NickEngmann/smarthome-reachy-mini/cad/crowpanel-advanced-7in-esp32-p4/preview.png

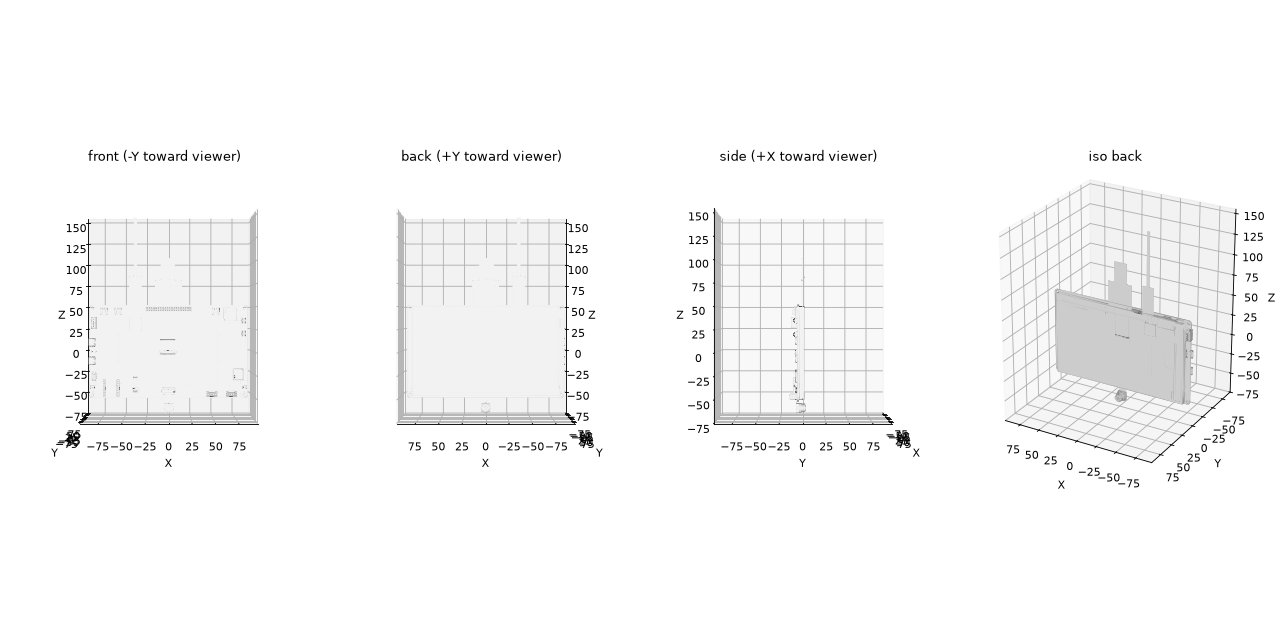
cad/crowpanel-advanced-7in-esp32-p4/preview.png
