NickEngmann/smarthome-reachy-mini/cad/reachy-mini/preview.png

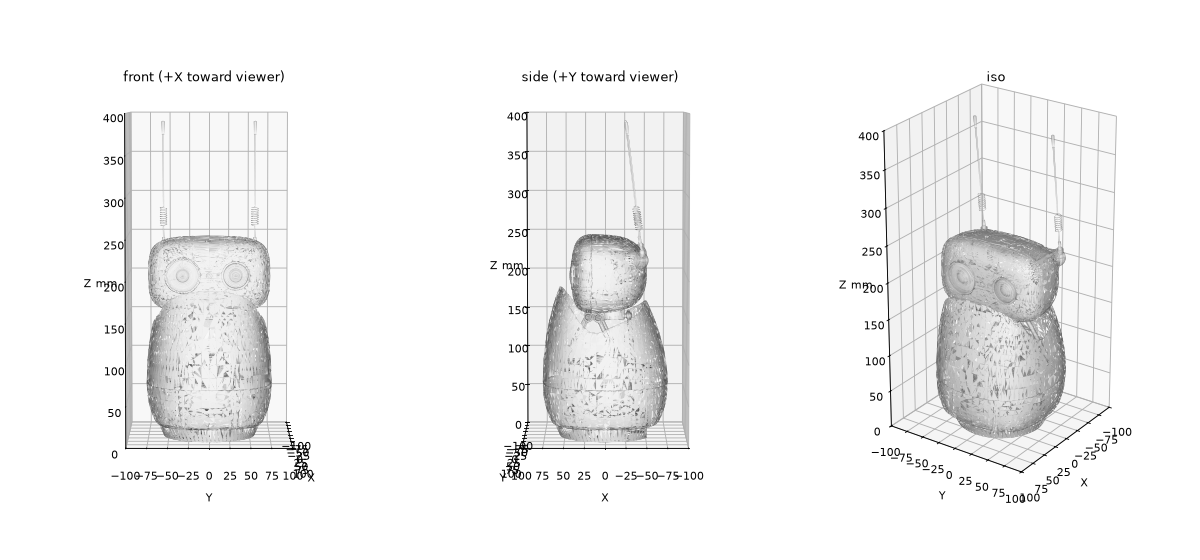
cad/reachy-mini/preview.png
