NickEngmann/smarthome-reachy-mini/hardware/enclosure/out/render/back-closeup.png

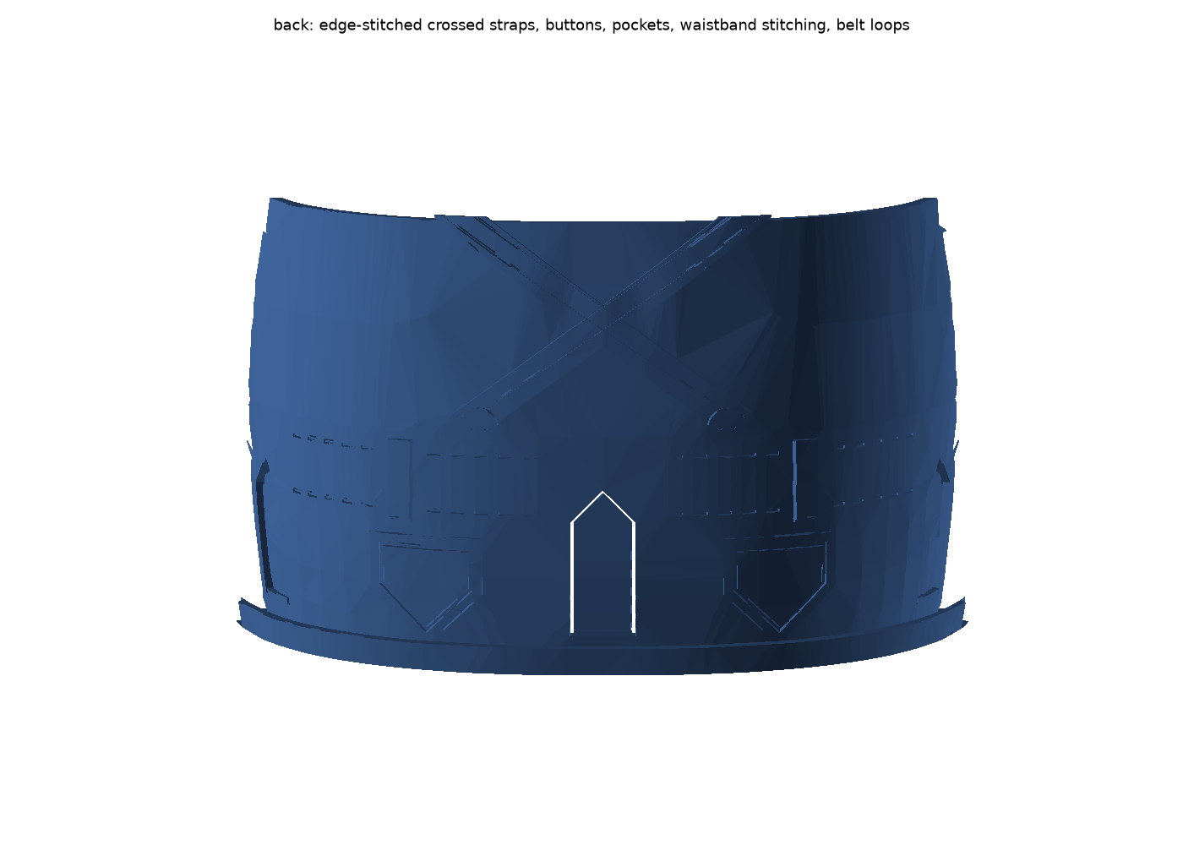
hardware/enclosure/out/render/back-closeup.png
