NickEngmann/smarthome-reachy-mini/hardware/enclosure/out/render/back-three-quarter.png

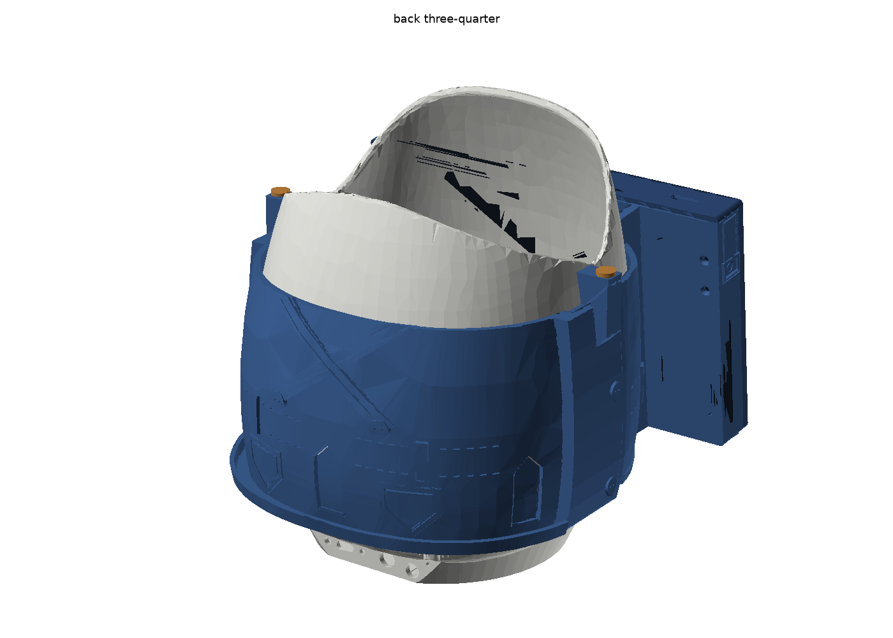
hardware/enclosure/out/render/back-three-quarter.png
