NickEngmann/smarthome-reachy-mini/hardware/enclosure/out/render/back.png

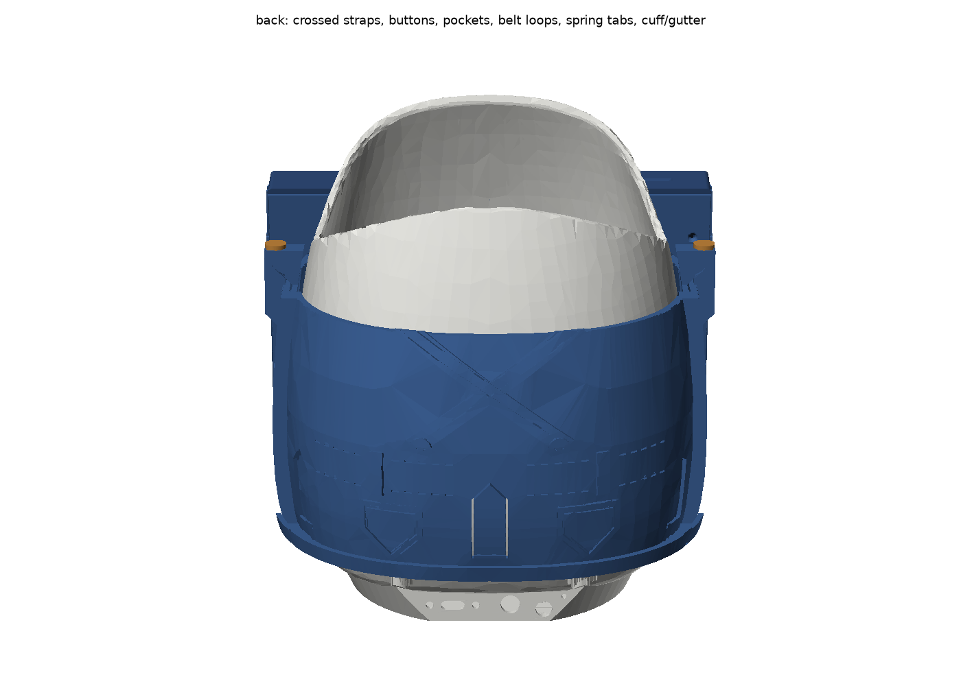
hardware/enclosure/out/render/back.png
