NickEngmann/smarthome-reachy-mini/hardware/enclosure/out/render/bib-closeup.png

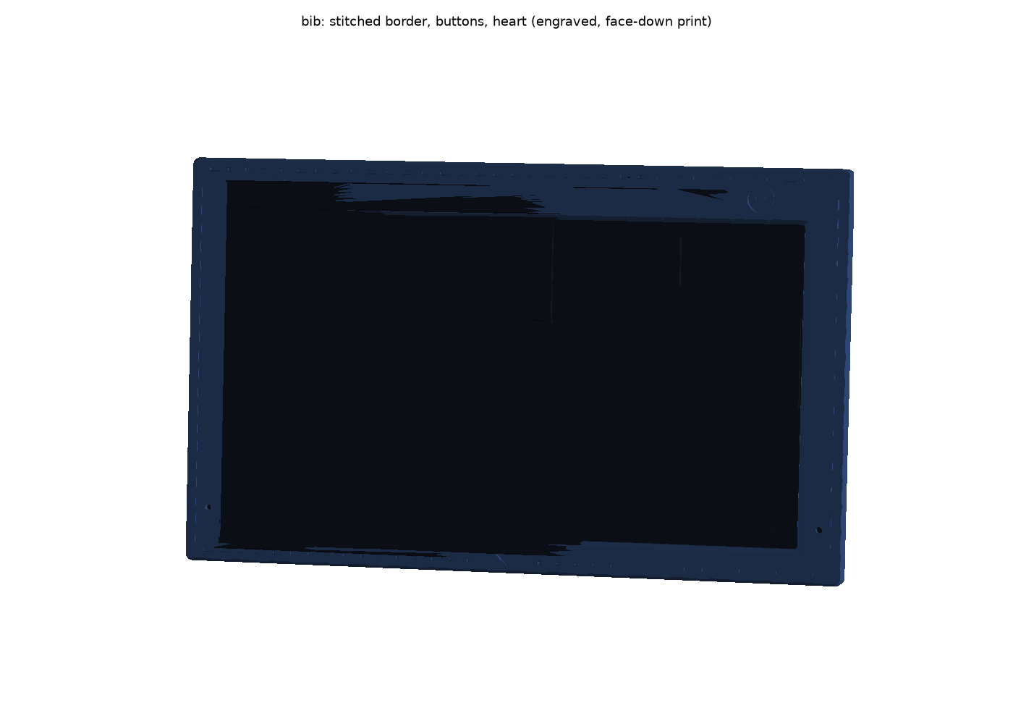
hardware/enclosure/out/render/bib-closeup.png
