NickEngmann/smarthome-reachy-mini/hardware/enclosure/out/render/exploded.png

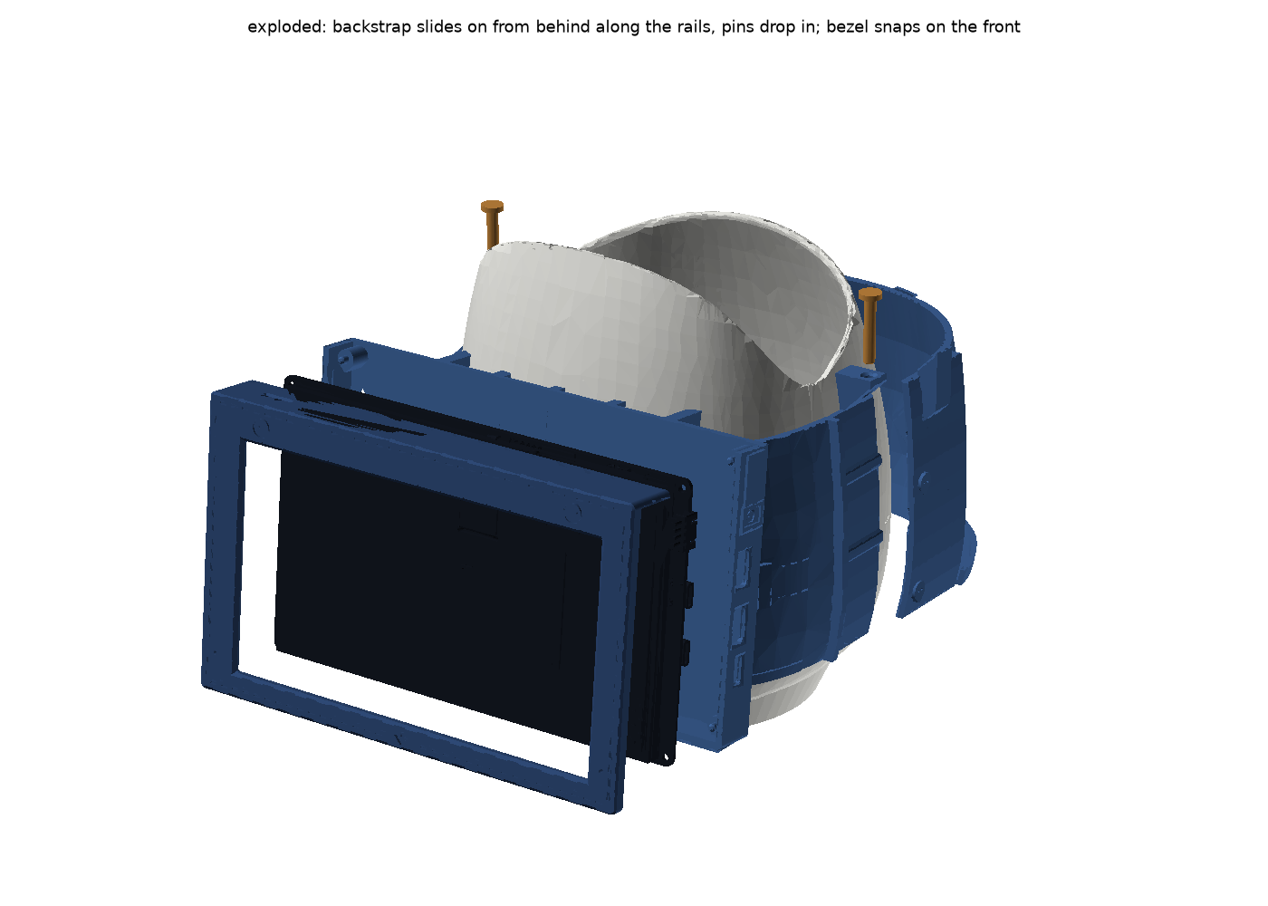
hardware/enclosure/out/render/exploded.png
