NickEngmann/smarthome-reachy-mini/hardware/enclosure/out/render/hero.png

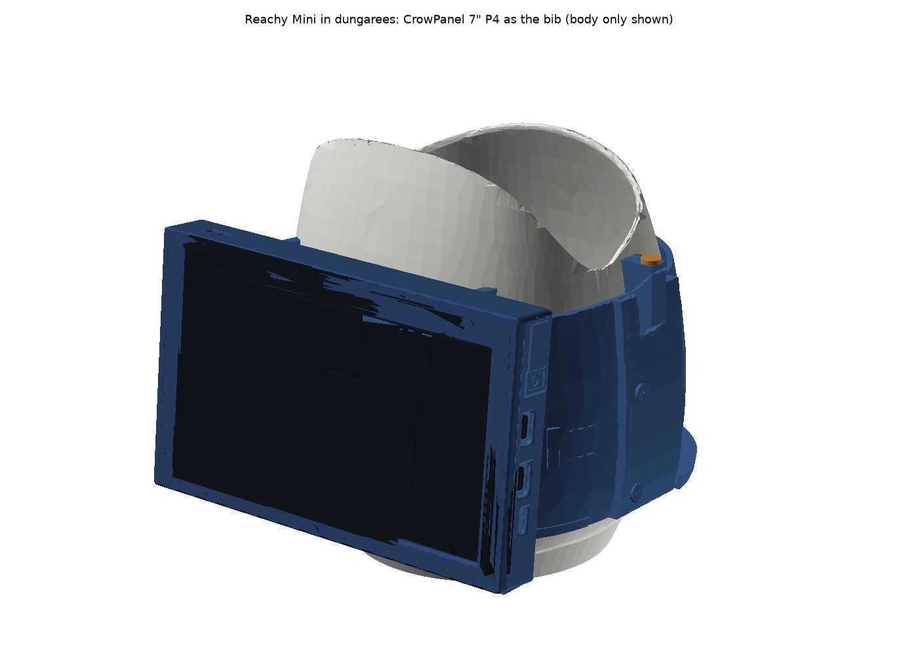
hardware/enclosure/out/render/hero.png
