NickEngmann/smarthome-reachy-mini/hardware/enclosure/out/render/joint-closeup.png

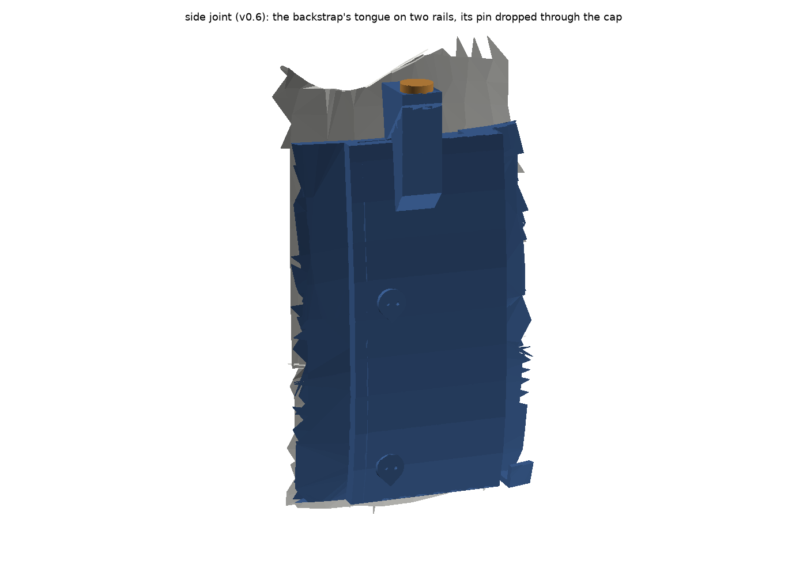
hardware/enclosure/out/render/joint-closeup.png
