NickEngmann/smarthome-reachy-mini/hardware/enclosure/out/render/joint-exploded.png

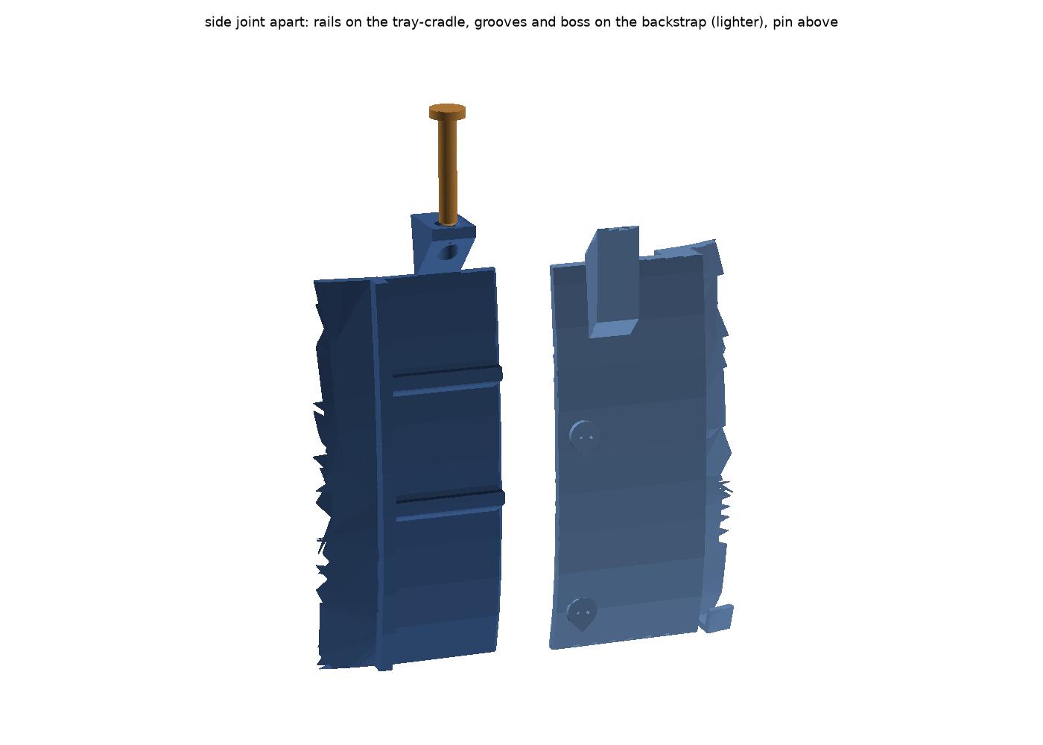
hardware/enclosure/out/render/joint-exploded.png
