NickEngmann/smarthome-reachy-mini/hardware/enclosure/out/render/overalls-cutaway-lifted.png

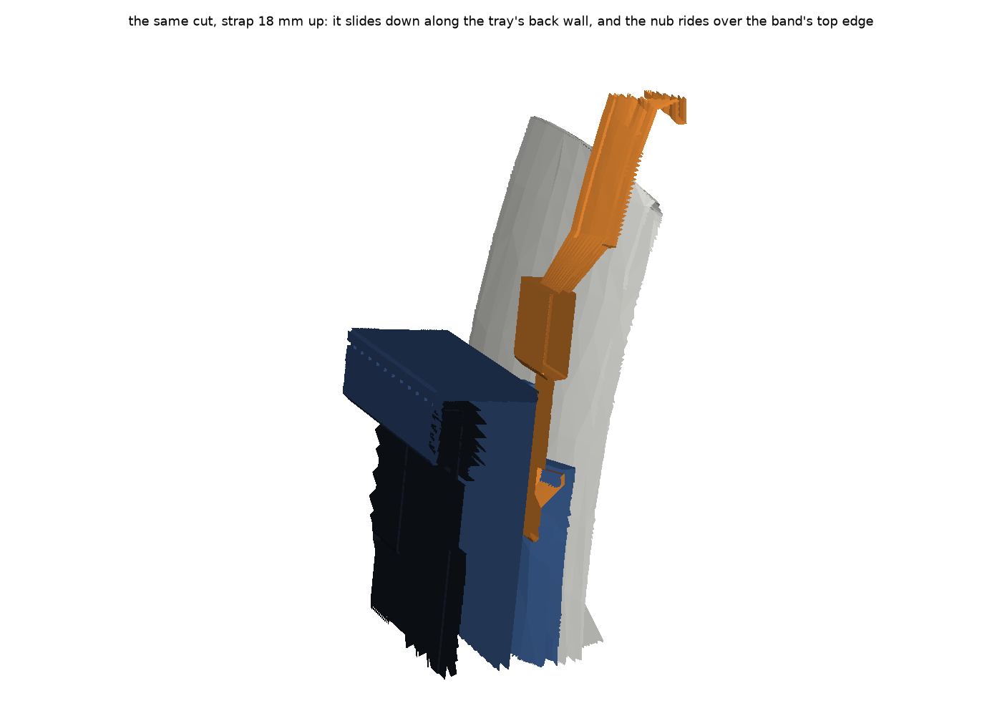
hardware/enclosure/out/render/overalls-cutaway-lifted.png
