NickEngmann/smarthome-reachy-mini/hardware/enclosure/out/render/overalls-fitting.png

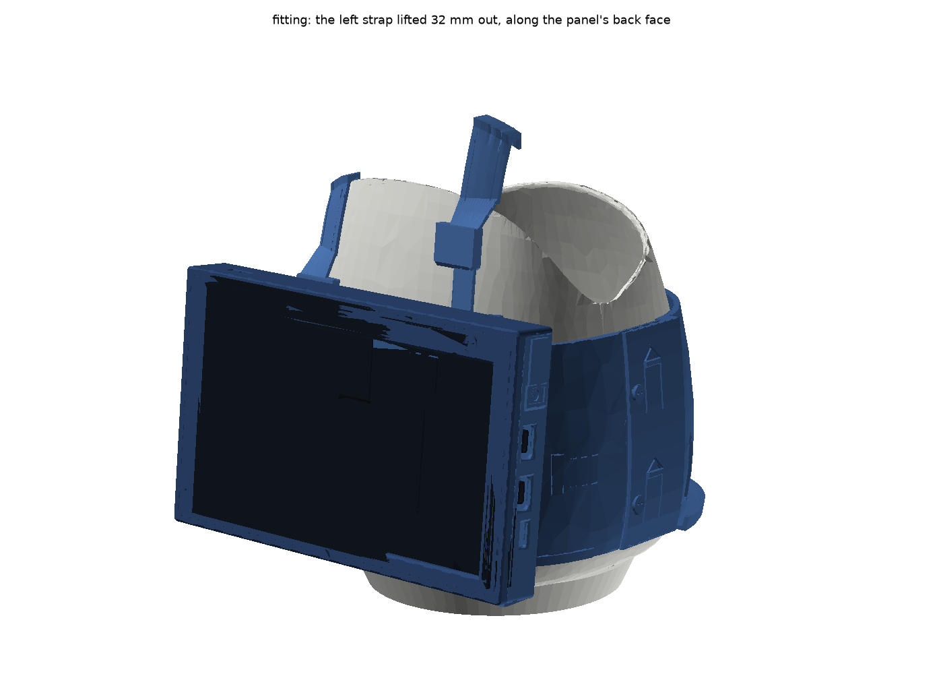
hardware/enclosure/out/render/overalls-fitting.png
