NickEngmann/smarthome-reachy-mini/hardware/enclosure/out/render/overalls-front.png

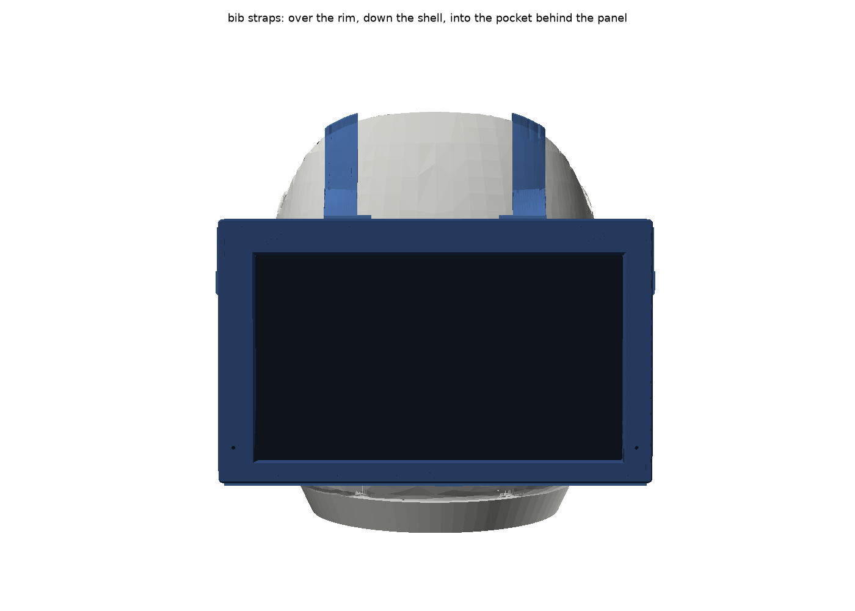
hardware/enclosure/out/render/overalls-front.png
