NickEngmann/smarthome-reachy-mini/hardware/enclosure/out/render/overalls-high.png

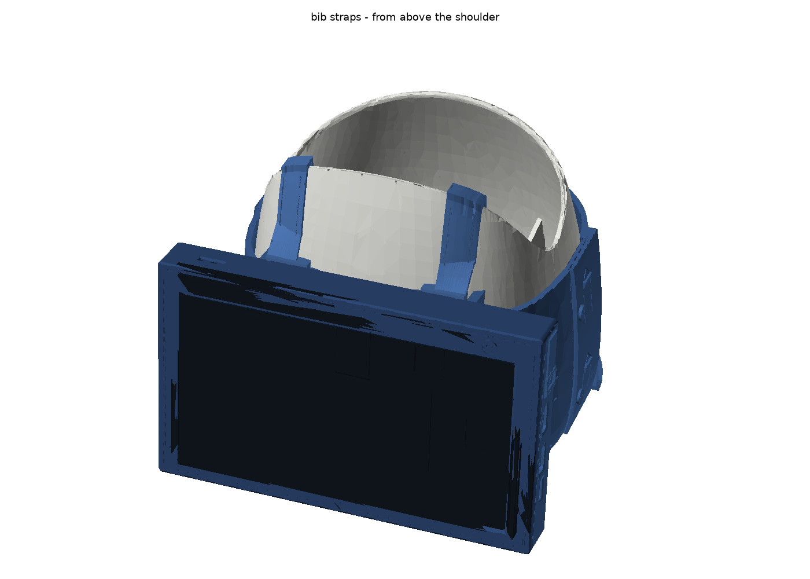
hardware/enclosure/out/render/overalls-high.png
