NickEngmann/smarthome-reachy-mini/hardware/enclosure/out/render/overalls-section-foot.png

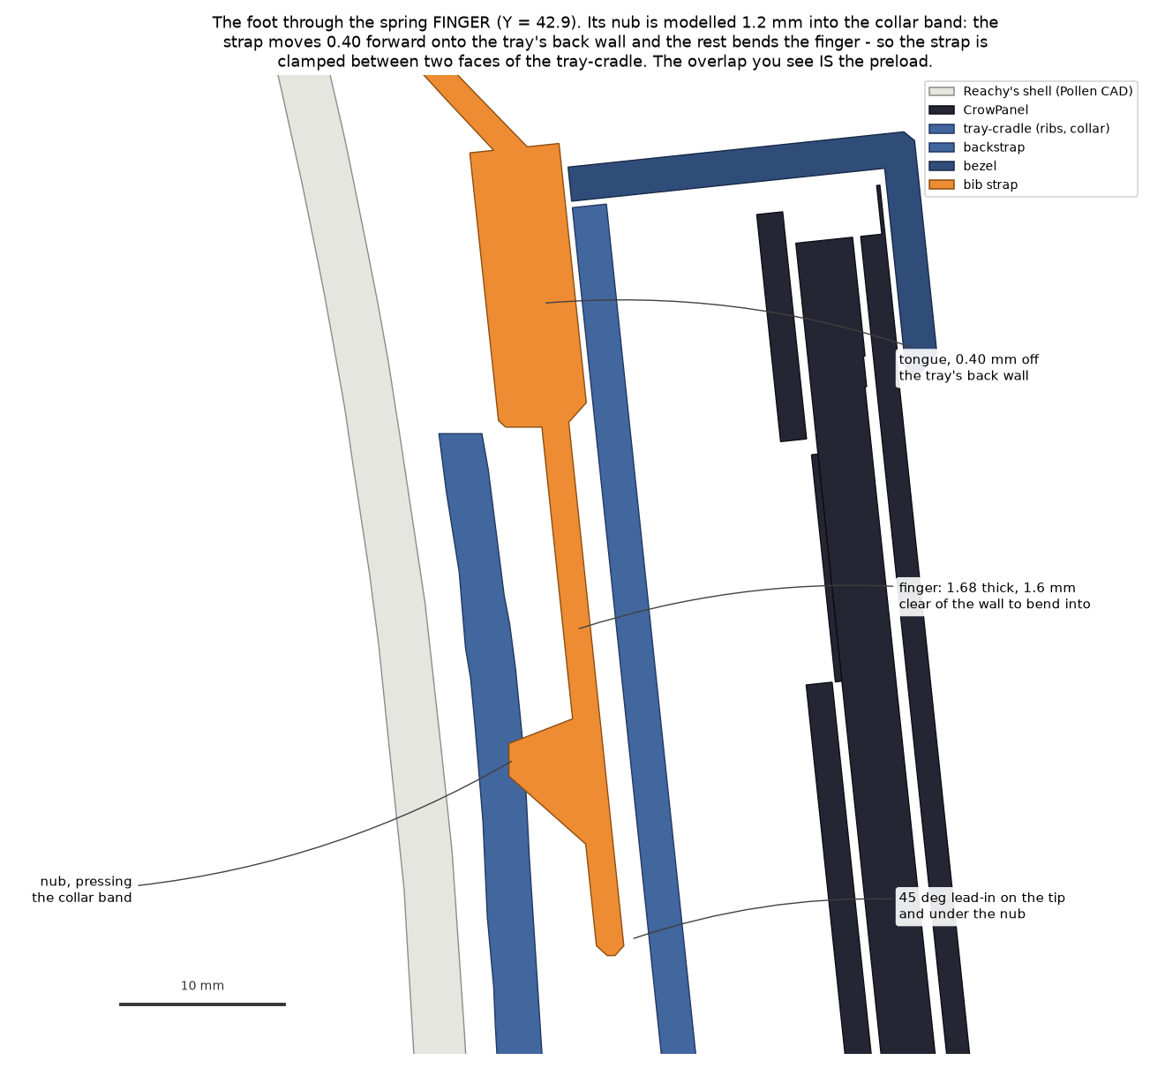
hardware/enclosure/out/render/overalls-section-foot.png
