NickEngmann/smarthome-reachy-mini/hardware/enclosure/out/render/overalls-section-rim.png

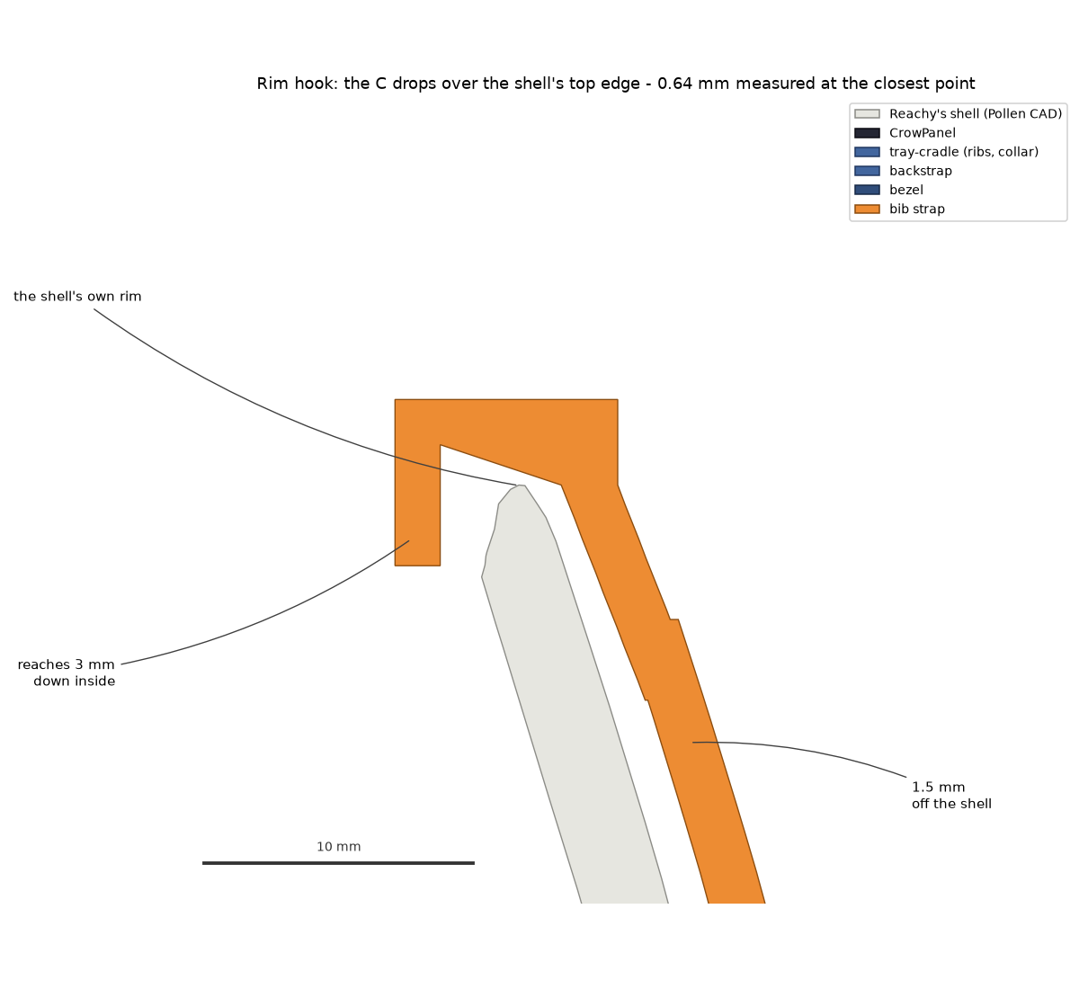
hardware/enclosure/out/render/overalls-section-rim.png
