NickEngmann/smarthome-reachy-mini/hardware/enclosure/out/render/overalls-section-tongue.png

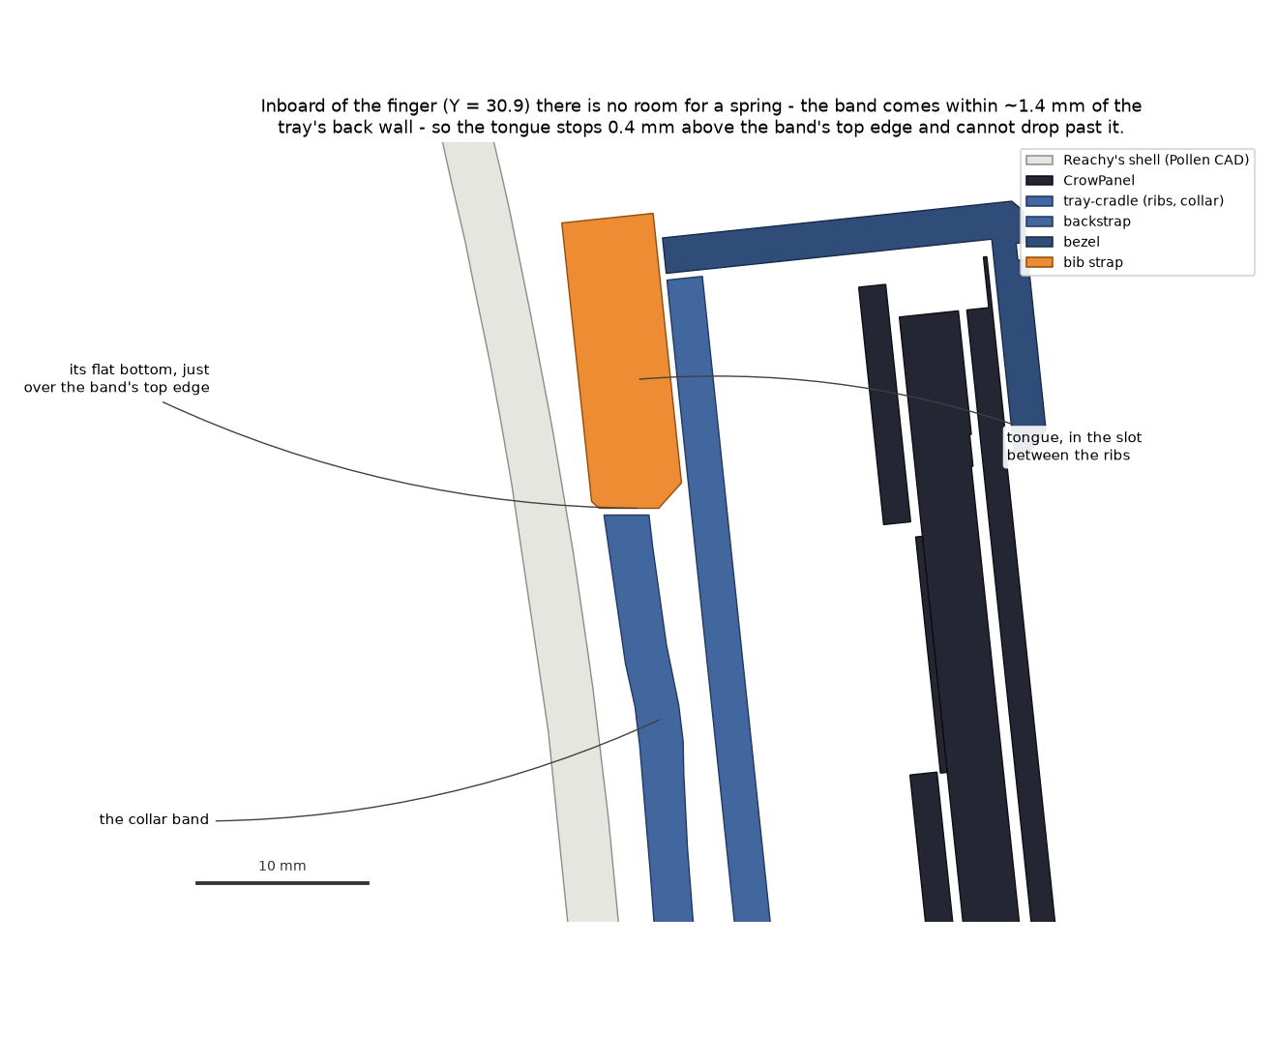
hardware/enclosure/out/render/overalls-section-tongue.png
