NickEngmann/smarthome-reachy-mini/hardware/enclosure/out/render/overalls-section.png

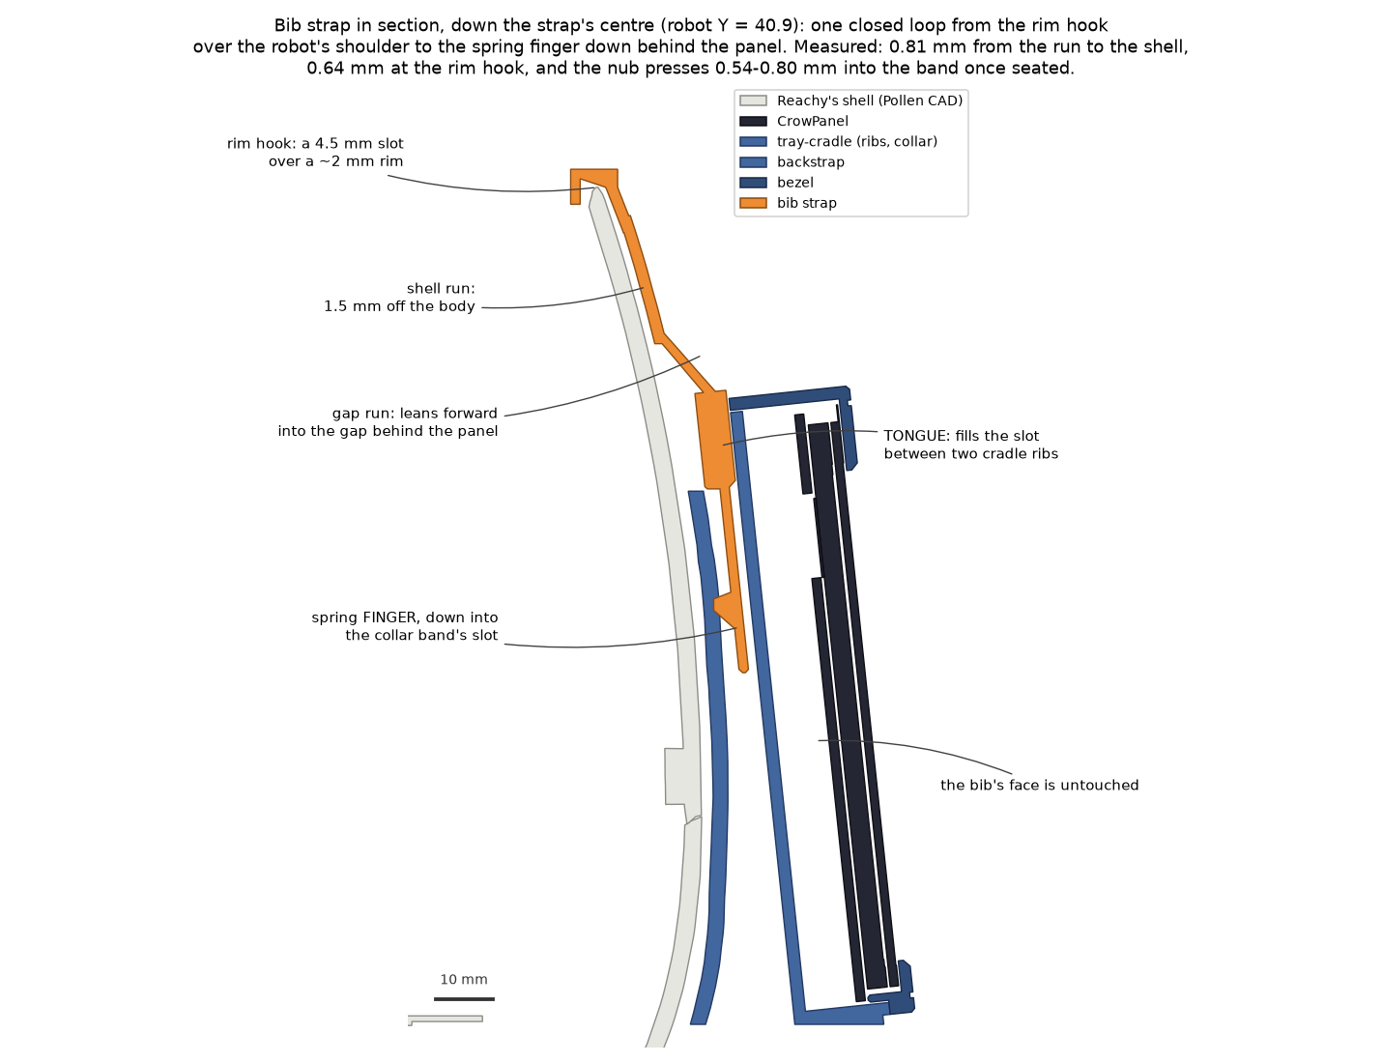
hardware/enclosure/out/render/overalls-section.png
