NickEngmann/smarthome-reachy-mini/hardware/enclosure/out/render/overalls-side.png

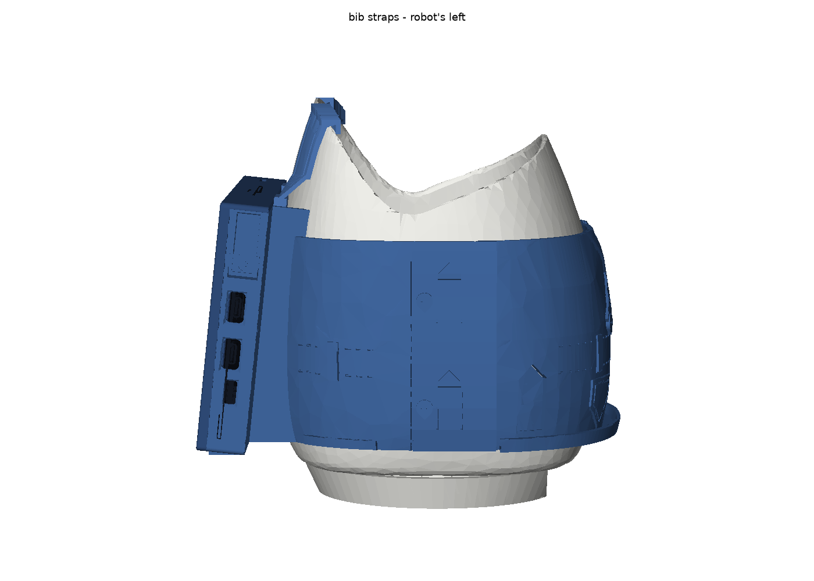
hardware/enclosure/out/render/overalls-side.png
