NickEngmann/smarthome-reachy-mini/cad/community-cases/acos-crowpanel-advance-7-enclosure-s3/acos-crowpanel-7-advance-rear.stl

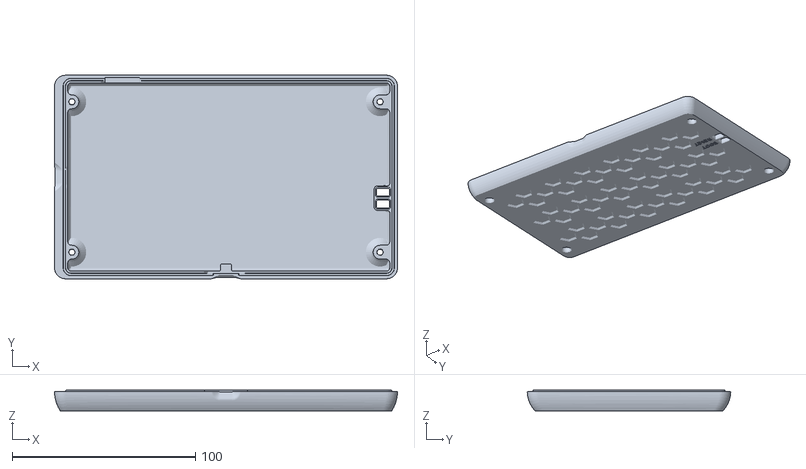
[picture p40: CAD file, 2026-09-13]
cad/community-cases/acos-crowpanel-advance-7-enclosure-s3/acos-crowpanel-7-advance-rear.stl
187.0 x 111.0 x 11.2
