NickEngmann/smarthome-reachy-mini/hardware/enclosure/out/print/reachy-crowpanel-bib-strap-left-print.stl

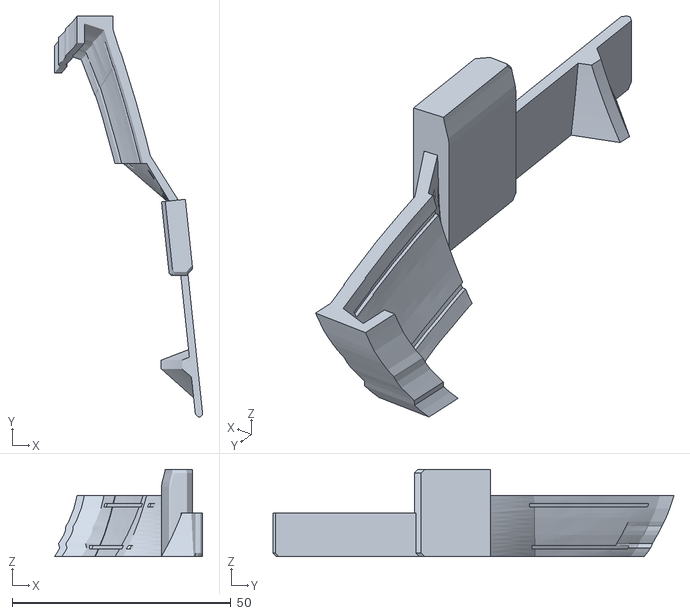
[picture p41: CAD file, 2026-09-30]
hardware/enclosure/out/print/reachy-crowpanel-bib-strap-left-print.stl
33.9 x 91.7 x 20.0
