NickEngmann/smarthome-reachy-mini/cad/community-cases/acos-crowpanel-advance-7-enclosure-s3/acos-crowpanel-7-advance-sma-usb-rear.stl

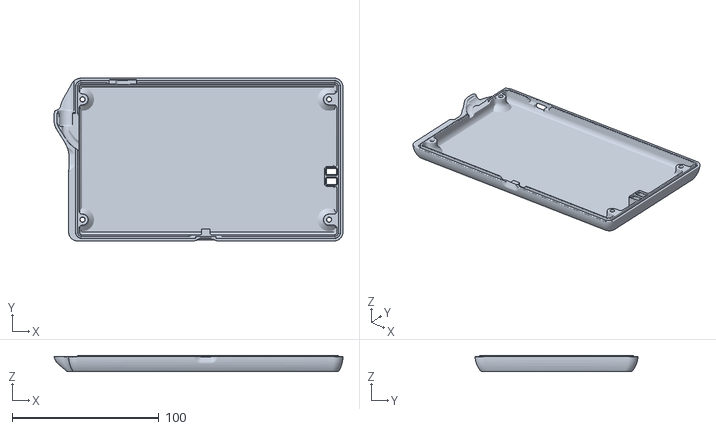
[picture p42: CAD file, 2026-09-13]
cad/community-cases/acos-crowpanel-advance-7-enclosure-s3/acos-crowpanel-7-advance-sma-usb-rear.stl
196.9 x 111.0 x 11.2
