NickEngmann/smarthome-reachy-mini/hardware/enclosure/out/print/reachy-crowpanel-bezel-print.stl

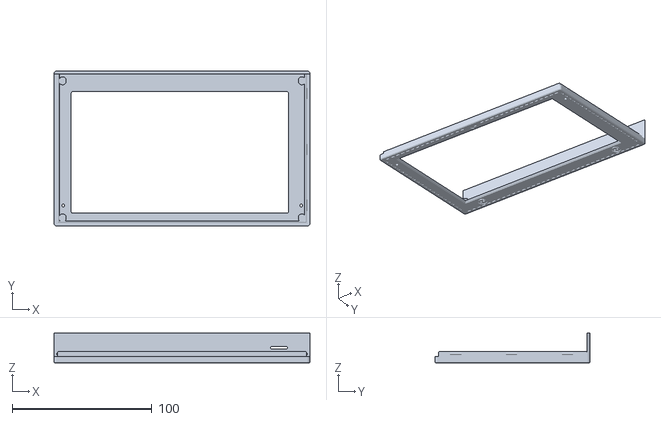
[picture p43: CAD file, 2026-09-20]
hardware/enclosure/out/print/reachy-crowpanel-bezel-print.stl
182.9 x 110.9 x 21.3
