NickEngmann/smarthome-reachy-mini/cad/community-cases/acos-crowpanel-advance-7-enclosure-s3/acos-crowpanel-7-advance-center.stl

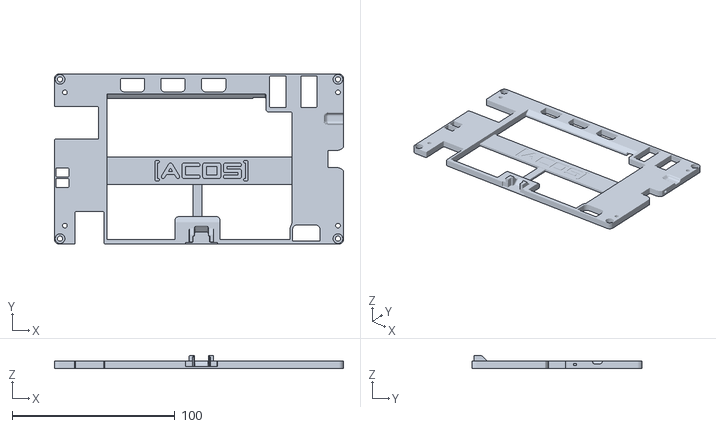
[picture p44: CAD file, 2026-09-13]
cad/community-cases/acos-crowpanel-advance-7-enclosure-s3/acos-crowpanel-7-advance-center.stl
177.8 x 104.8 x 7.80
