NickEngmann/smarthome-reachy-mini/hardware/enclosure/out/render/print-backstrap.png

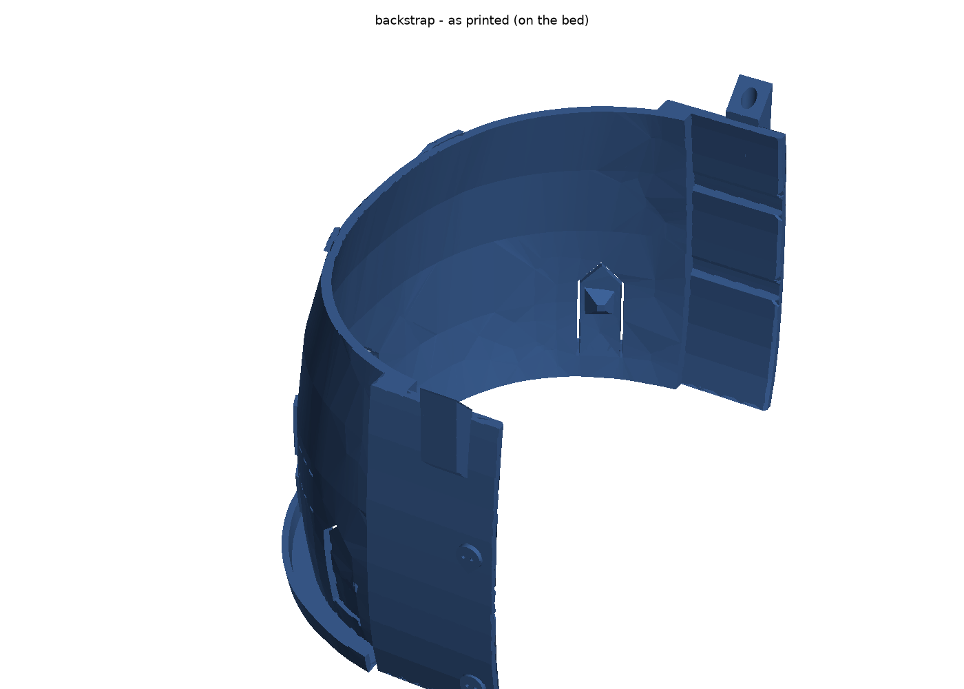
hardware/enclosure/out/render/print-backstrap.png
