NickEngmann/smarthome-reachy-mini/hardware/enclosure/out/render/print-bezel.png

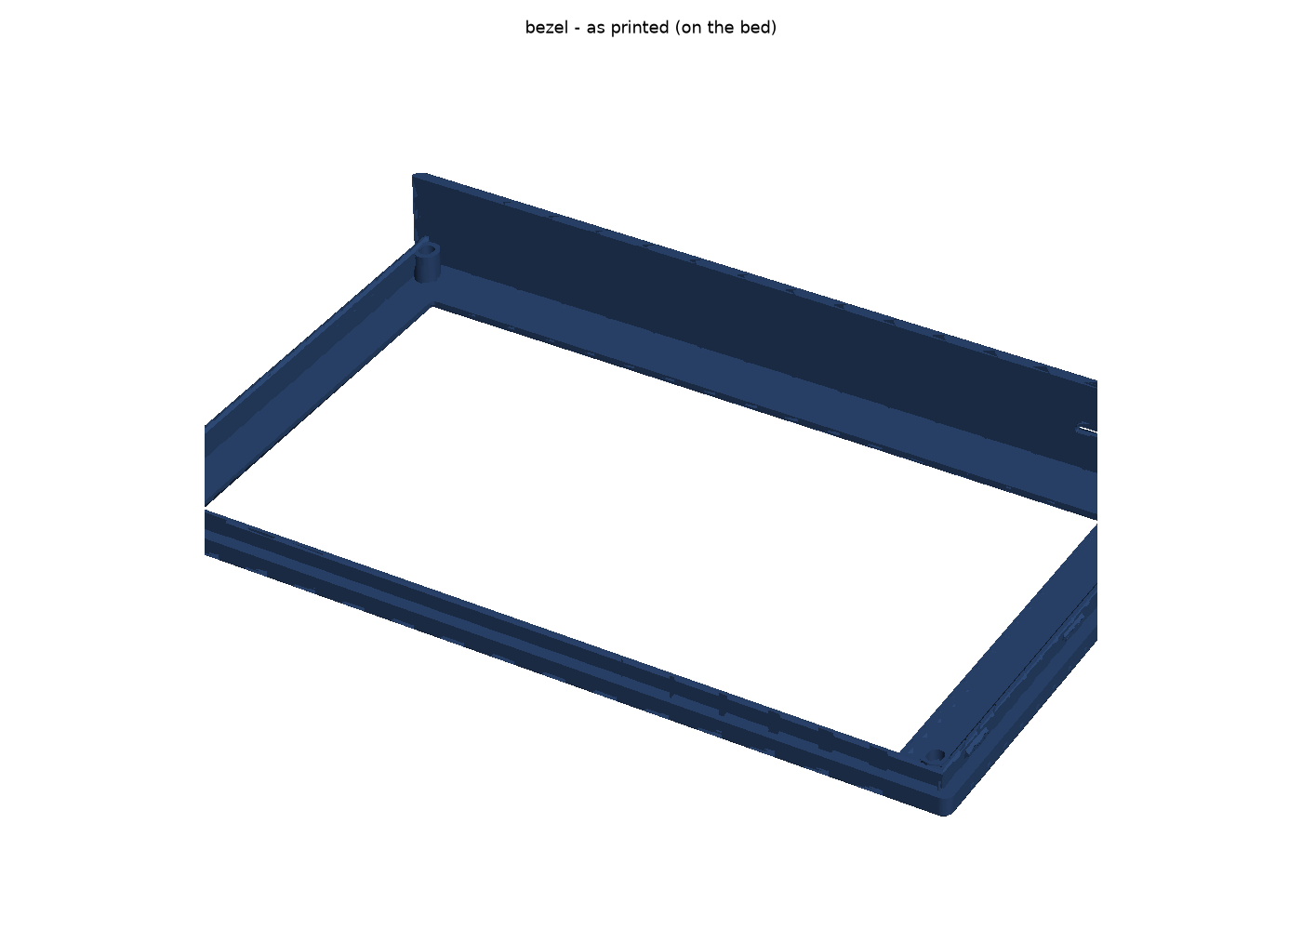
hardware/enclosure/out/render/print-bezel.png
