NickEngmann/smarthome-reachy-mini/hardware/enclosure/out/render/print-bib-strap-left.png

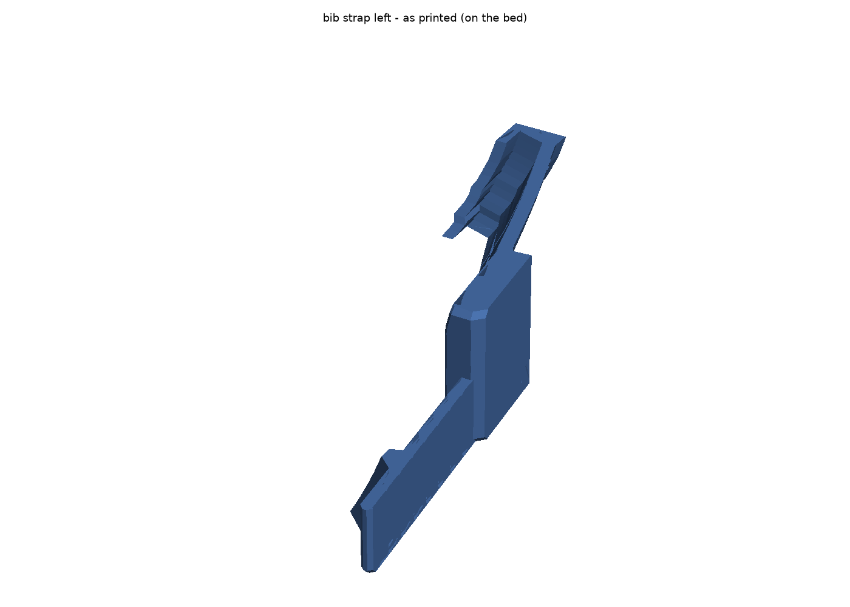
hardware/enclosure/out/render/print-bib-strap-left.png
