NickEngmann/smarthome-reachy-mini/hardware/enclosure/out/render/print-bib-strap-right.png

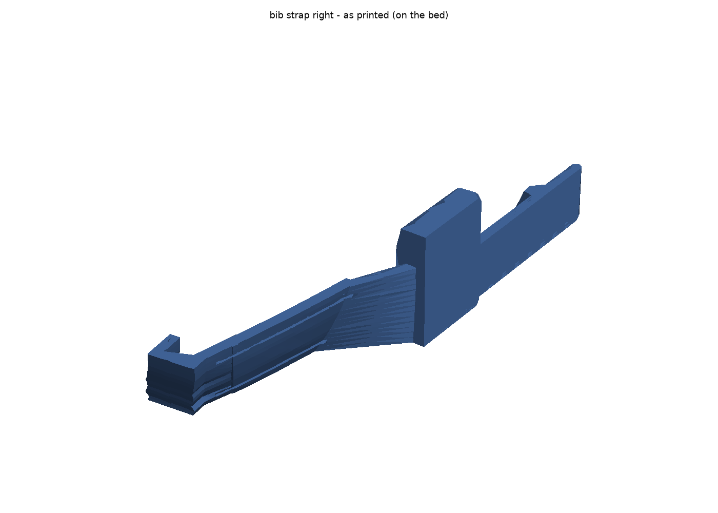
hardware/enclosure/out/render/print-bib-strap-right.png
