NickEngmann/smarthome-reachy-mini/hardware/enclosure/out/render/print-pins.png

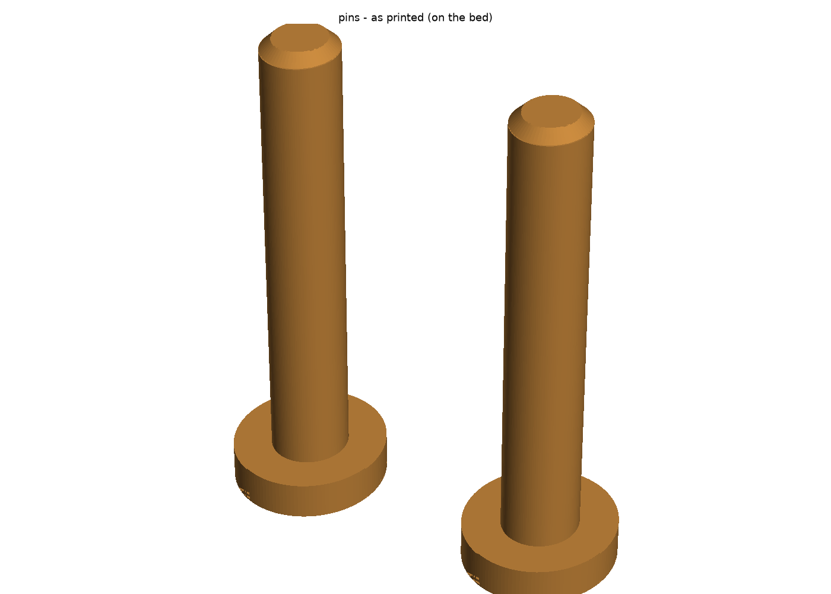
hardware/enclosure/out/render/print-pins.png
