NickEngmann/smarthome-reachy-mini/hardware/enclosure/out/render/print-tray-cradle.png

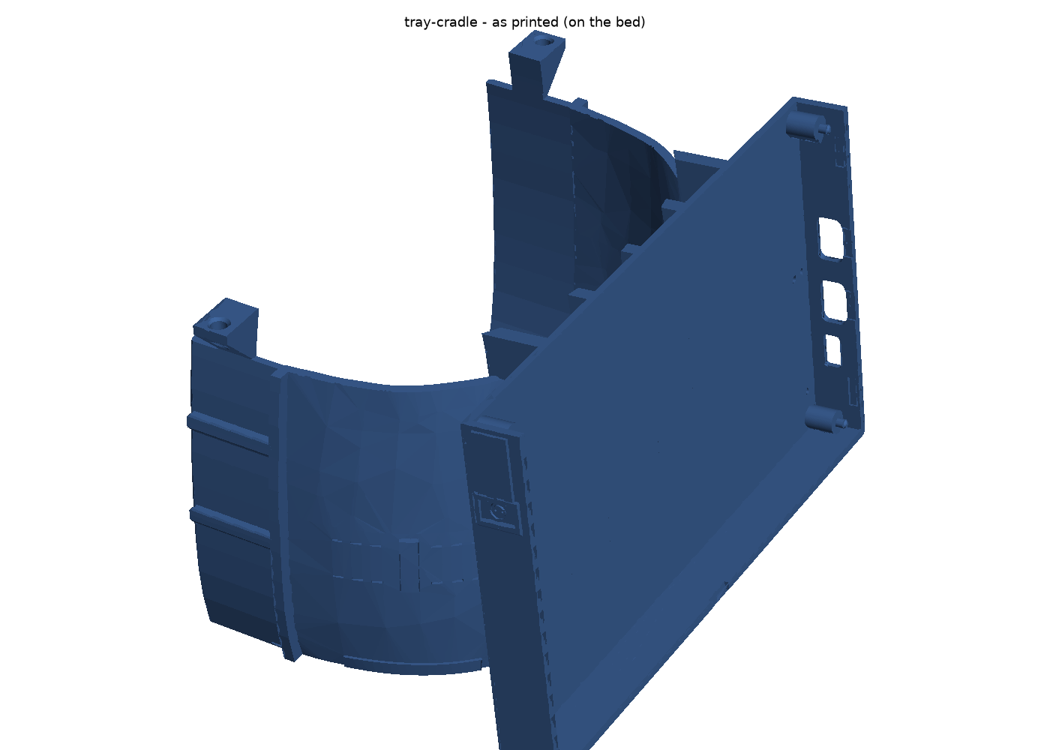
hardware/enclosure/out/render/print-tray-cradle.png
